BigBIueWhale/sanwu_lasers_magnet_connector/docs/amazon_magnet_diameter_not_as_advertized.jpg

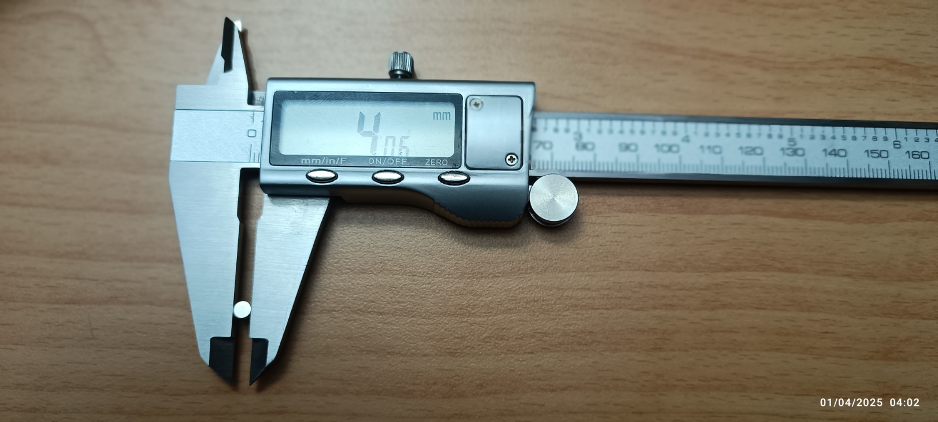
docs/amazon_magnet_diameter_not_as_advertized.jpg
