BigBIueWhale/sanwu_lasers_magnet_connector/docs/bad_super_glue_brand.jpg

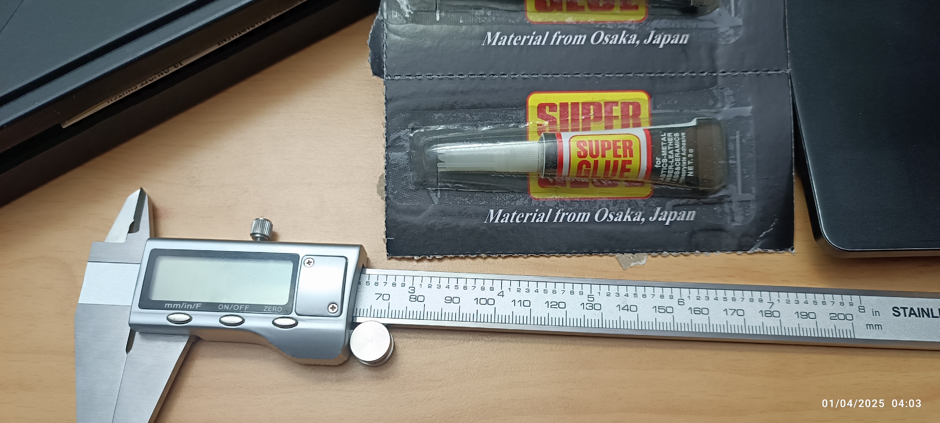
docs/bad_super_glue_brand.jpg
