BigBIueWhale/sanwu_lasers_magnet_connector/docs/gain_leverage.jpg

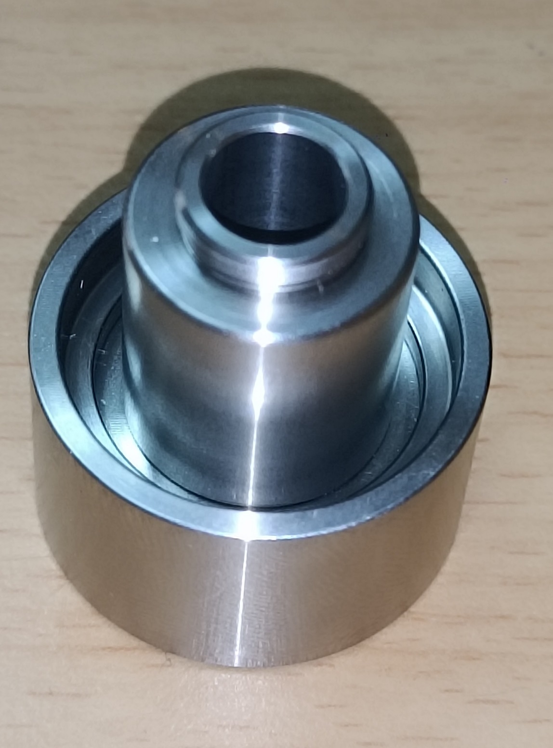
docs/gain_leverage.jpg
