BigBIueWhale/sanwu_lasers_magnet_connector/docs/generic_custom_part_paint_3d_view.png

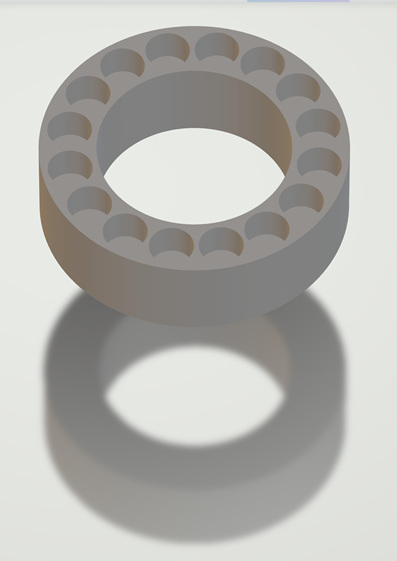
docs/generic_custom_part_paint_3d_view.png
