BigBIueWhale/sanwu_lasers_magnet_connector/docs/good_super_glue_brand.jpg

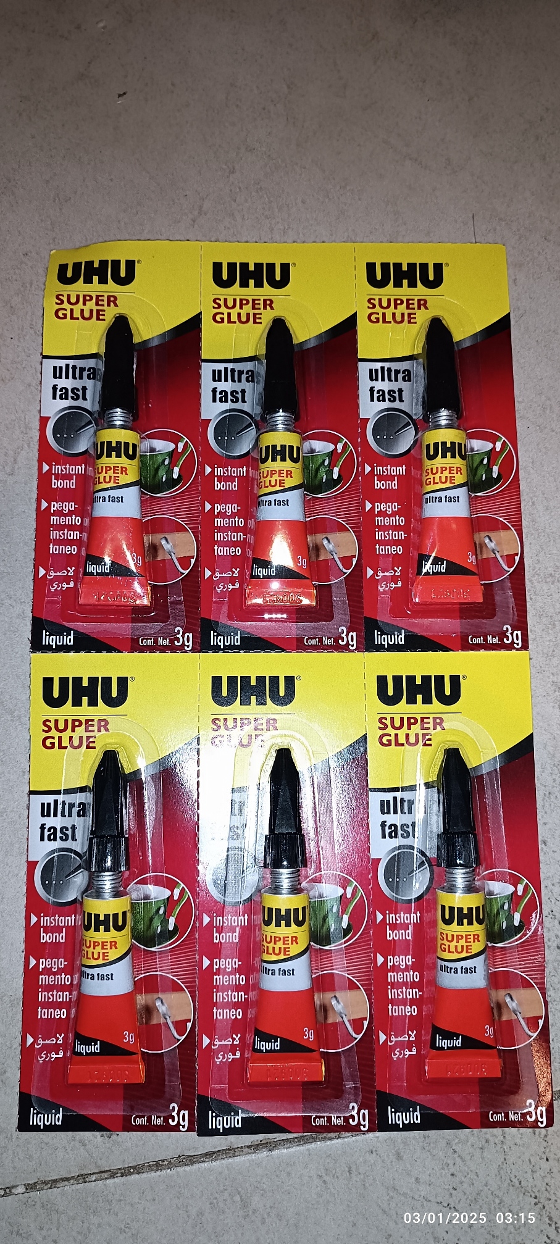
docs/good_super_glue_brand.jpg
