BigBIueWhale/sanwu_lasers_magnet_connector/docs/guard_sleeve_01_00_01_area_to_wipe.jpg

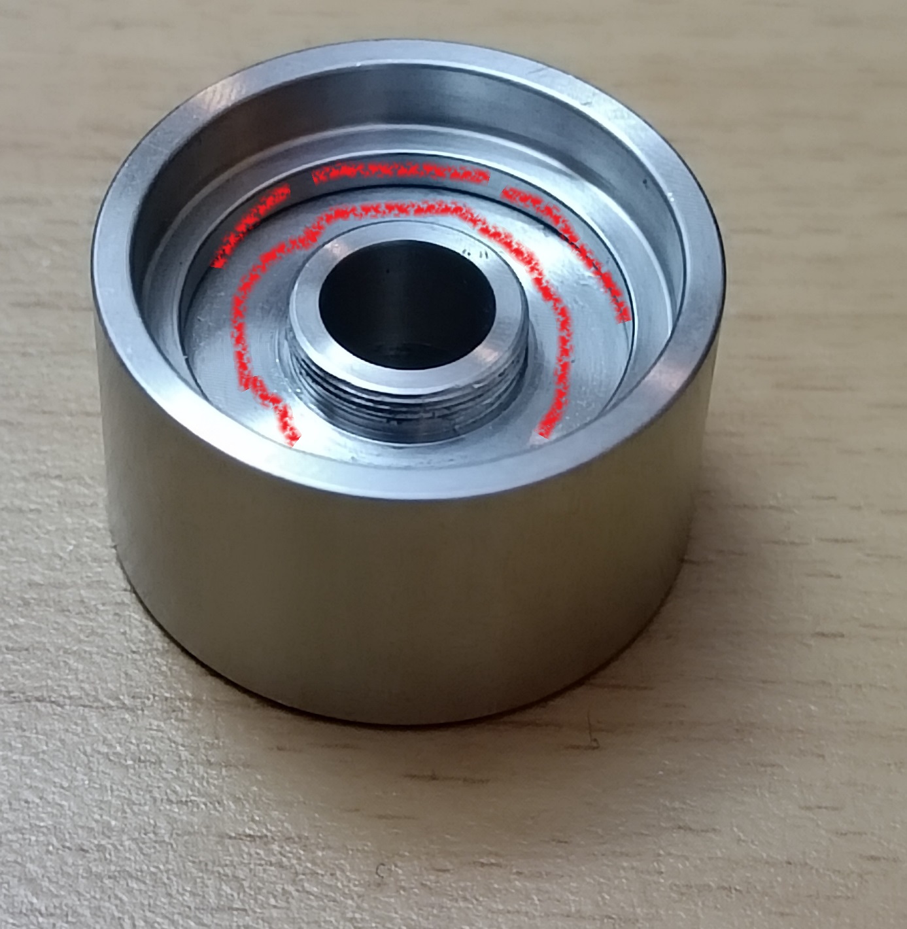
docs/guard_sleeve_01_00_01_area_to_wipe.jpg
