BigBIueWhale/sanwu_lasers_magnet_connector/docs/guard_sleeve_01_00_01_inside_of_bottom_ring.jpg

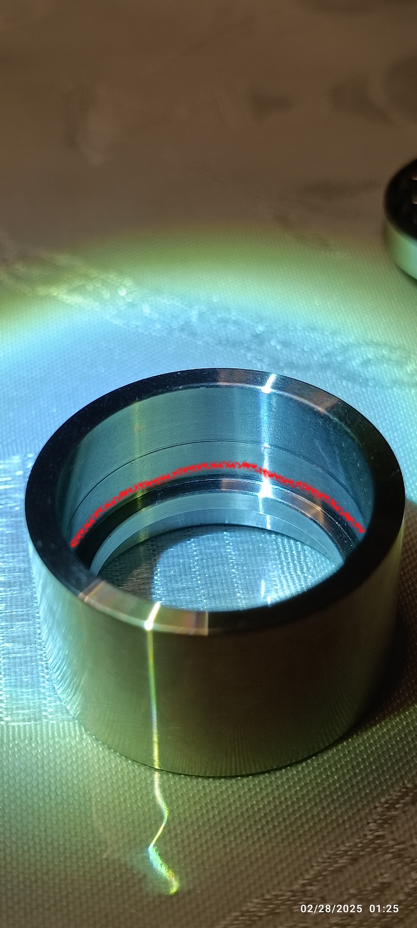
docs/guard_sleeve_01_00_01_inside_of_bottom_ring.jpg
