BigBIueWhale/sanwu_lasers_magnet_connector/docs/guard_sleeve_01_00_01_rangers_head.jpg

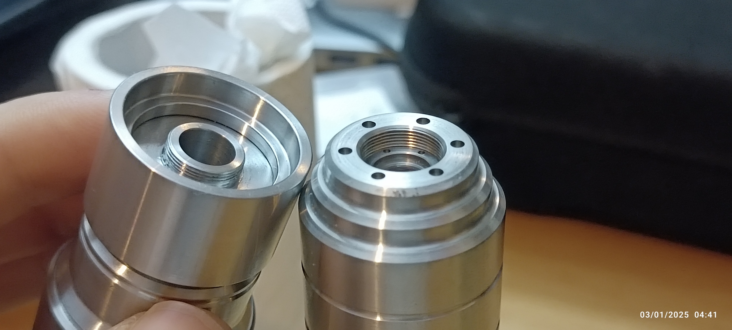
docs/guard_sleeve_01_00_01_rangers_head.jpg
