BigBIueWhale/sanwu_lasers_magnet_connector/docs/laser_and_flashlight_adapter.jpg

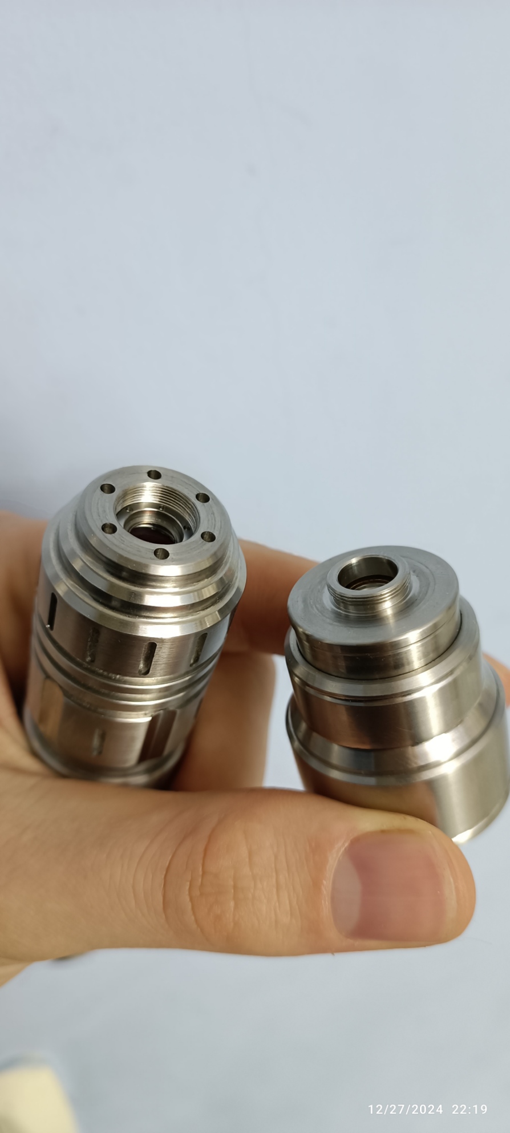
docs/laser_and_flashlight_adapter.jpg
