BigBIueWhale/sanwu_lasers_magnet_connector/docs/laser_rangers_body_models.png

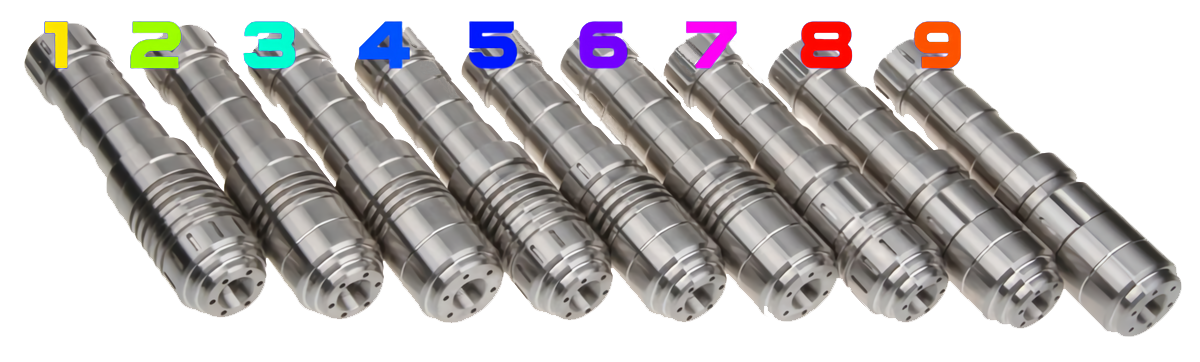
docs/laser_rangers_body_models.png
