BigBIueWhale/sanwu_lasers_magnet_connector/docs/magnets_and_xometry_magnet_holes.jpg

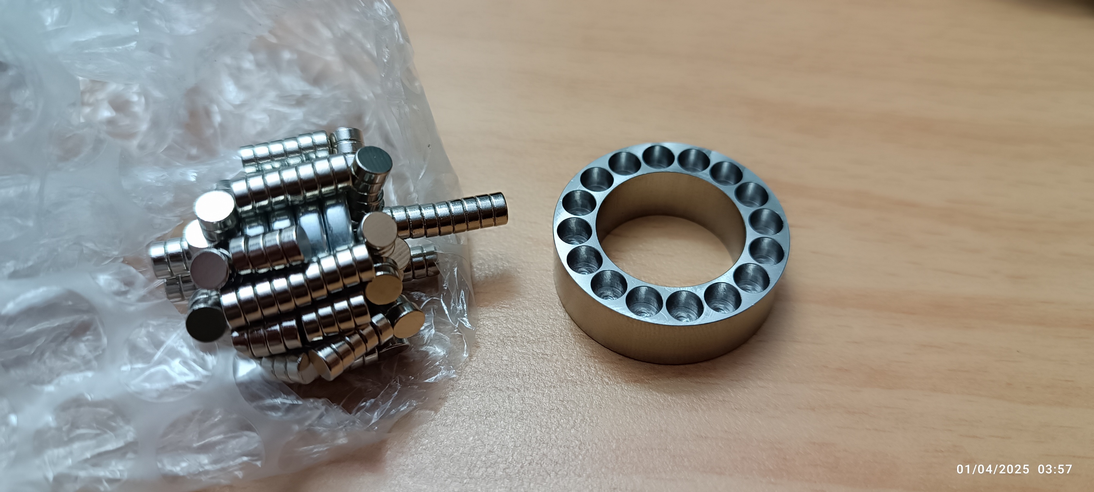
docs/magnets_and_xometry_magnet_holes.jpg
