BigBIueWhale/sanwu_lasers_magnet_connector/docs/magnets_box_findmag.jpg

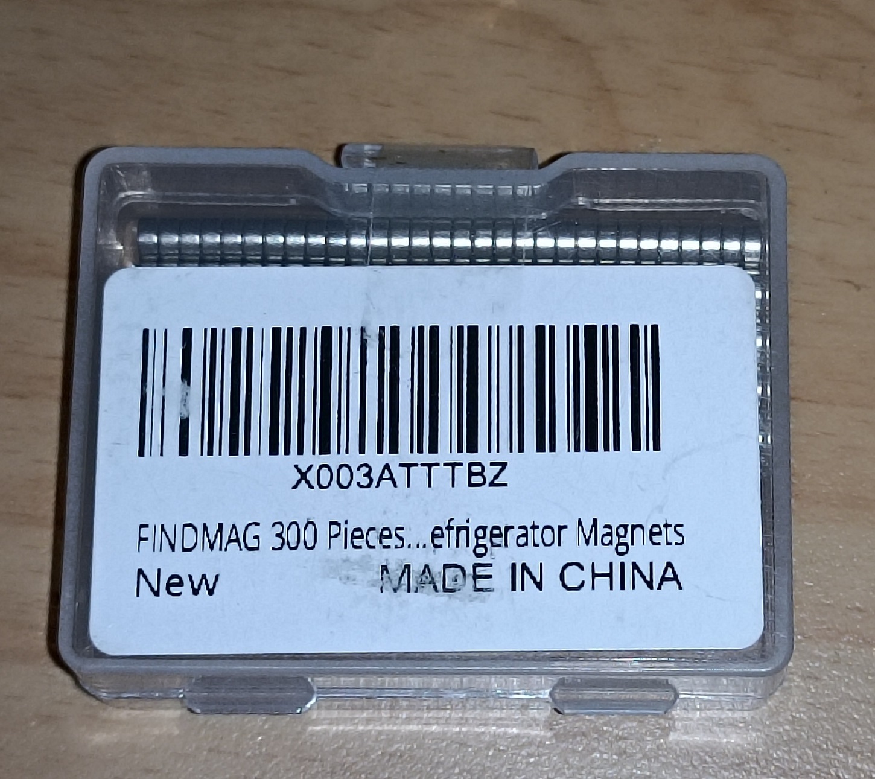
docs/magnets_box_findmag.jpg
