BigBIueWhale/sanwu_lasers_magnet_connector/docs/neodymium_magnets_amazon_listing.png

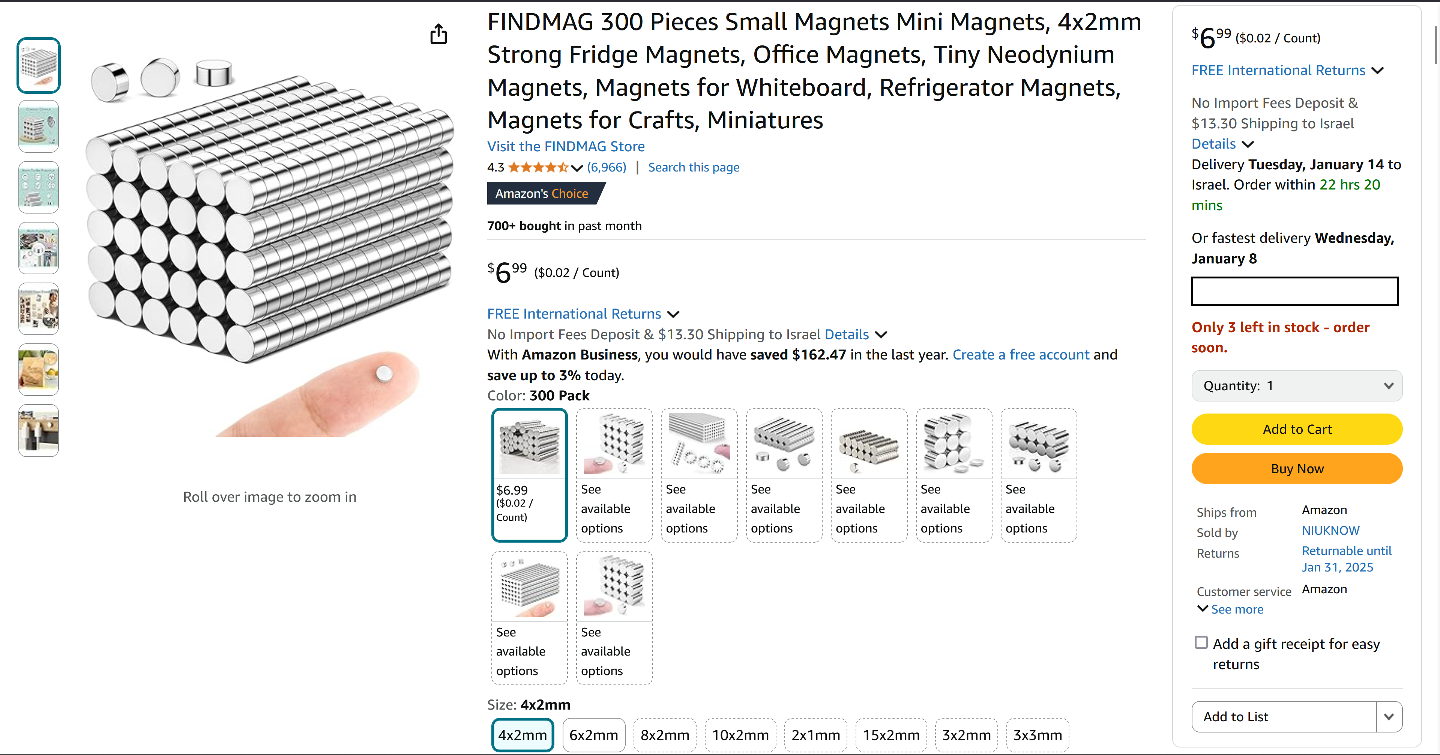
docs/neodymium_magnets_amazon_listing.png
