BigBIueWhale/sanwu_lasers_magnet_connector/docs/pcbway_choose_stainless_steel_303.png

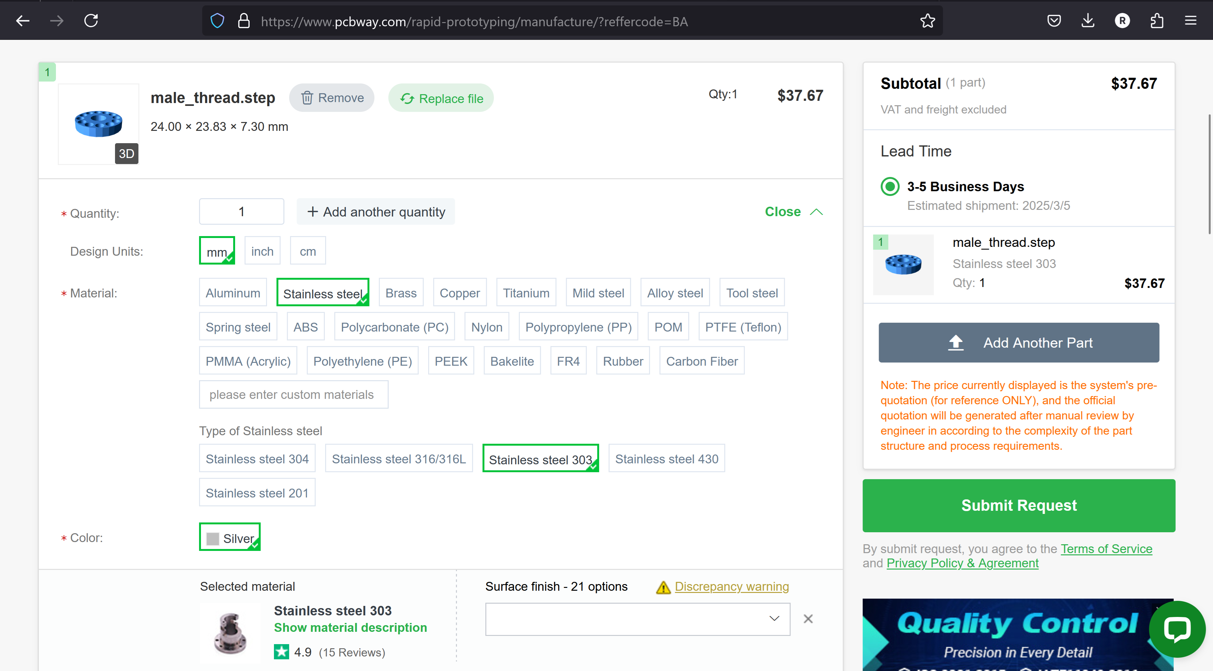
docs/pcbway_choose_stainless_steel_303.png
