BigBIueWhale/sanwu_lasers_magnet_connector/docs/pcbway_click_yes_on_threads_and_tapped_holes.png

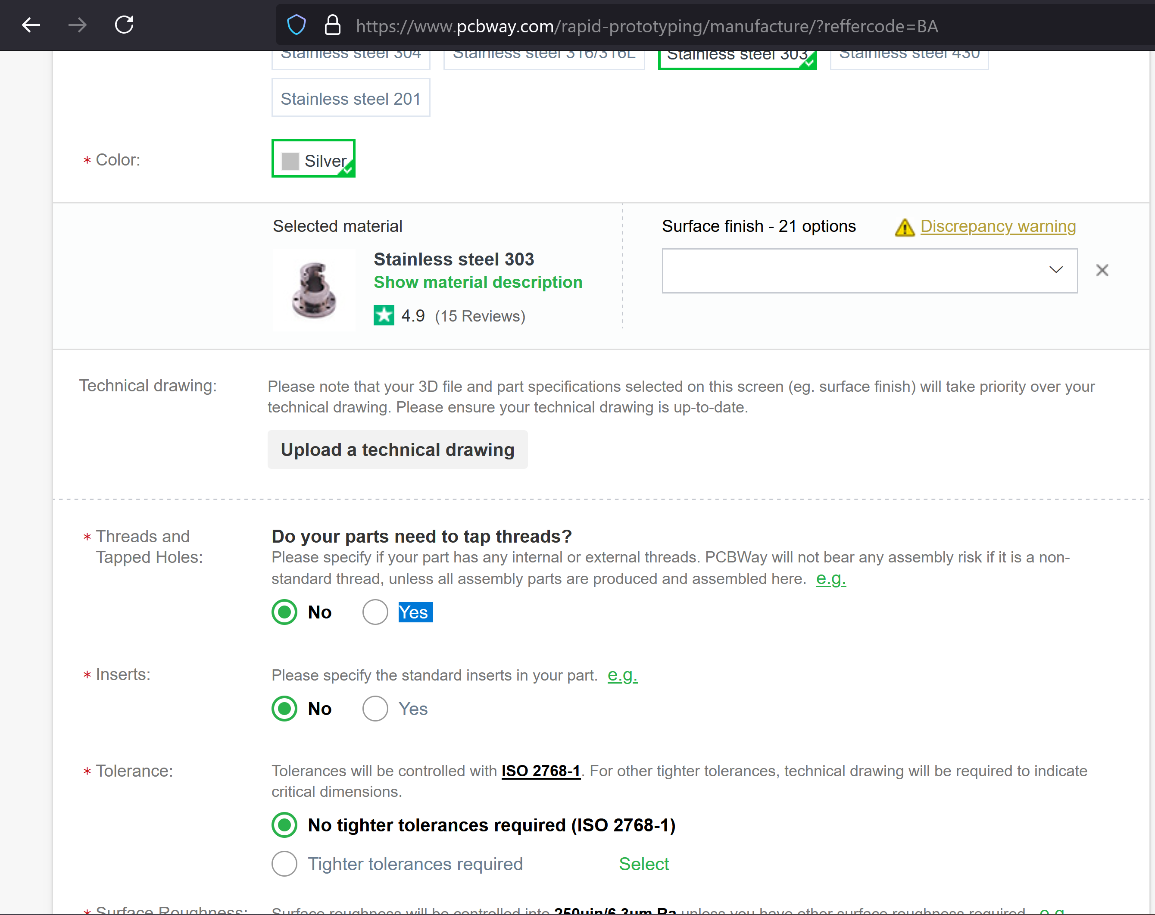
docs/pcbway_click_yes_on_threads_and_tapped_holes.png
