BigBIueWhale/sanwu_lasers_magnet_connector/docs/pcbway_cnc_machining_upload.png

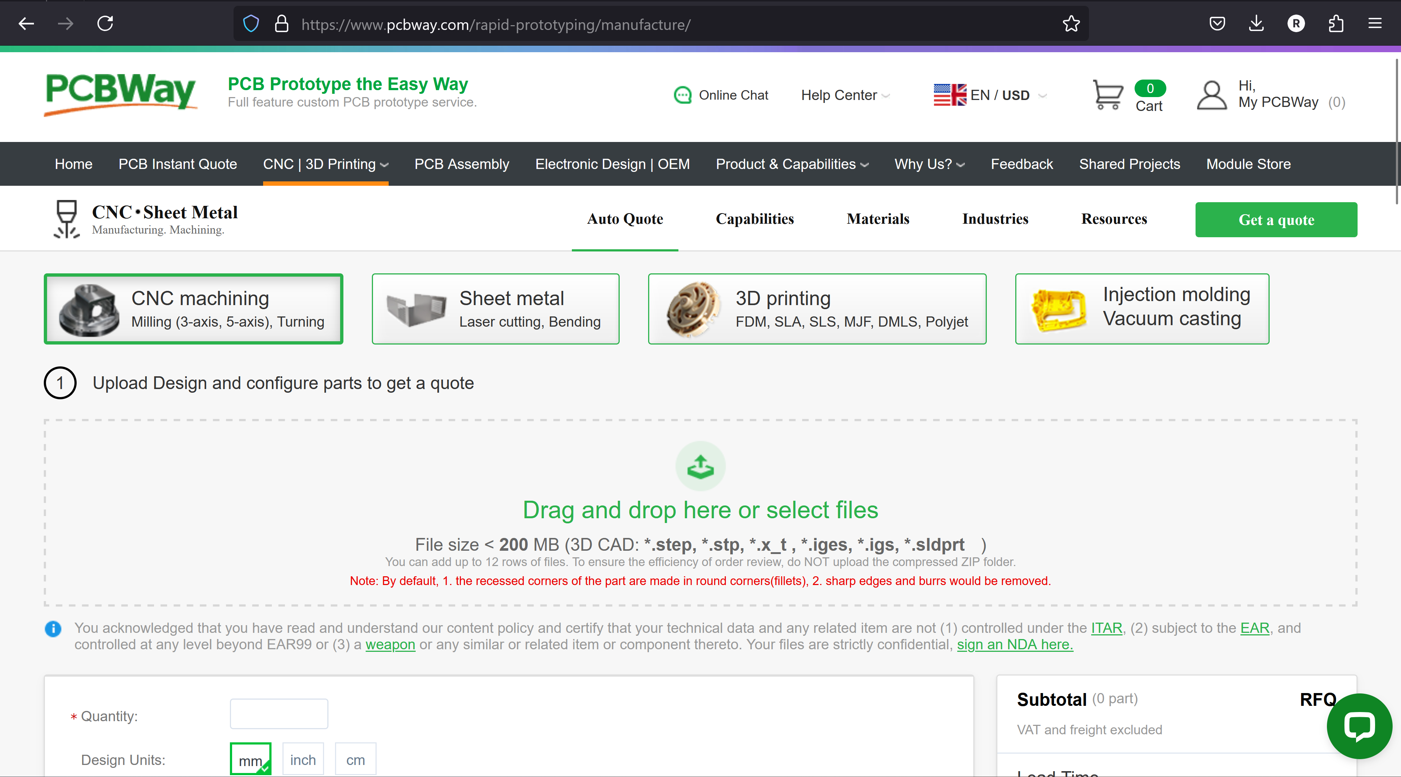
docs/pcbway_cnc_machining_upload.png
