BigBIueWhale/sanwu_lasers_magnet_connector/docs/pcbway_female_thread_01_00_00_raw.jpg

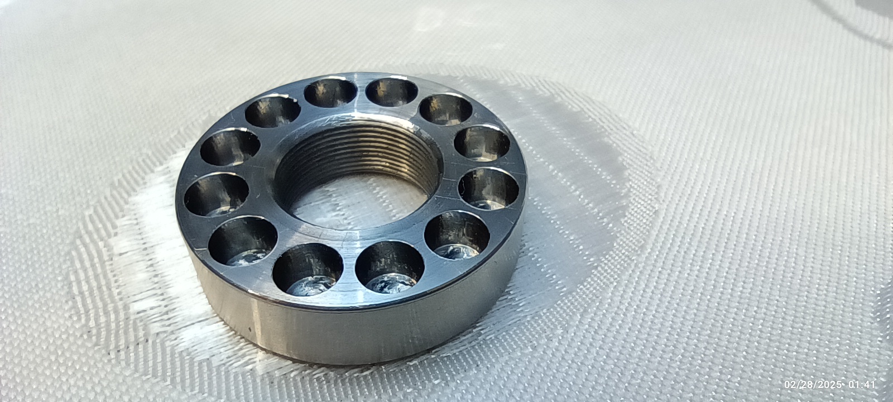
docs/pcbway_female_thread_01_00_00_raw.jpg
