BigBIueWhale/sanwu_lasers_magnet_connector/docs/pcbway_magnet_holes_and_guard_sleeve.jpg

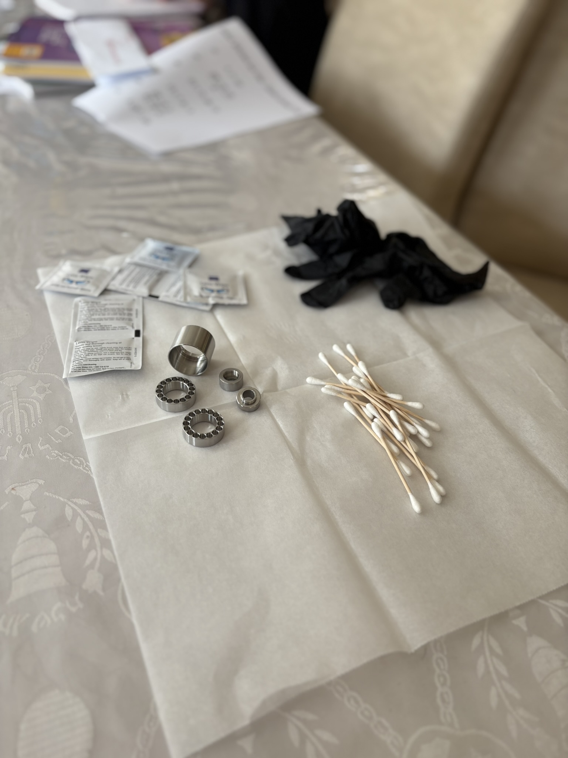
docs/pcbway_magnet_holes_and_guard_sleeve.jpg
