BigBIueWhale/sanwu_lasers_magnet_connector/docs/pcbway_male_female_threads_01_00_00_raw.jpg

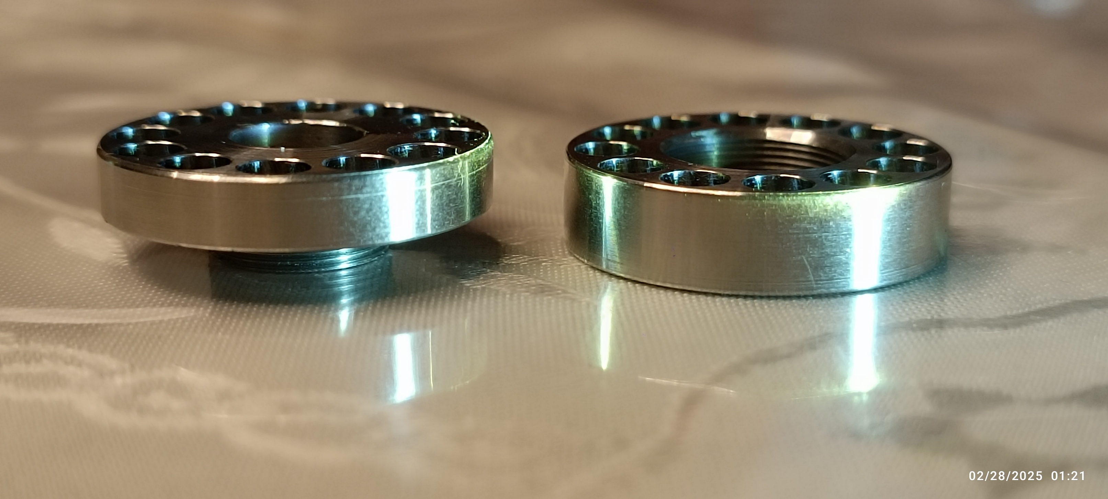
docs/pcbway_male_female_threads_01_00_00_raw.jpg
