BigBIueWhale/sanwu_lasers_magnet_connector/docs/pcbway_male_thread_01_00_00_raw.jpg

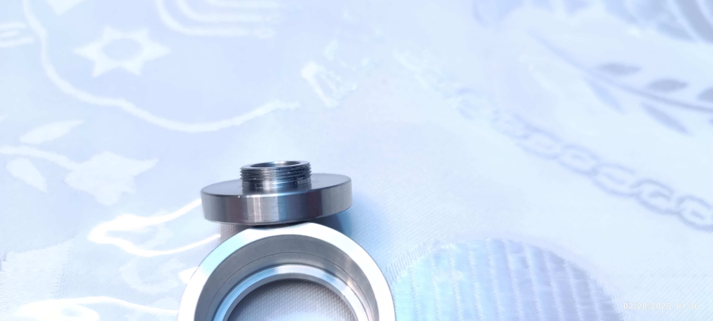
docs/pcbway_male_thread_01_00_00_raw.jpg
