BigBIueWhale/sanwu_lasers_magnet_connector/docs/pcbway_ready_to_submit_request.png

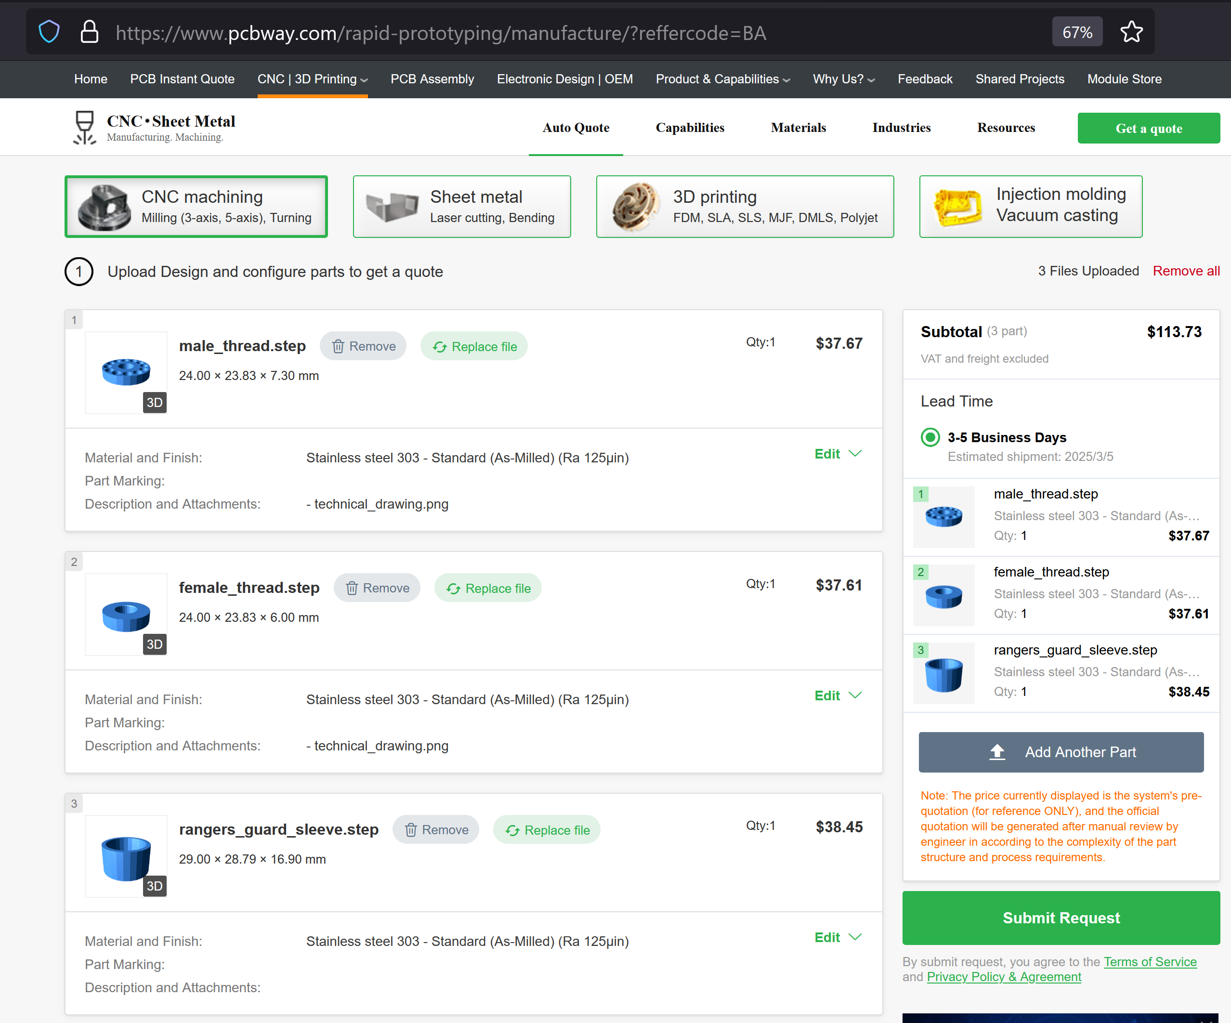
docs/pcbway_ready_to_submit_request.png
