BigBIueWhale/sanwu_lasers_magnet_connector/docs/pcbway_upload_technical_drawing.png

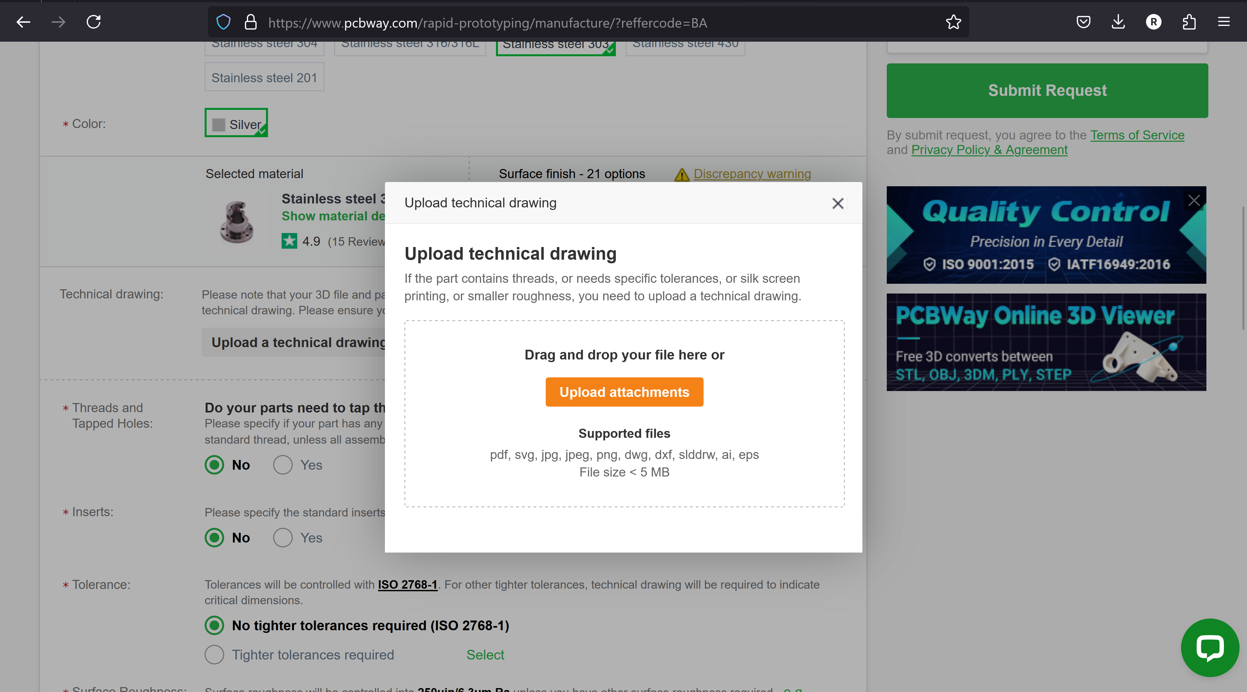
docs/pcbway_upload_technical_drawing.png
