BigBIueWhale/sanwu_lasers_magnet_connector/docs/sanwu_adapter_cut_in_half.jpg

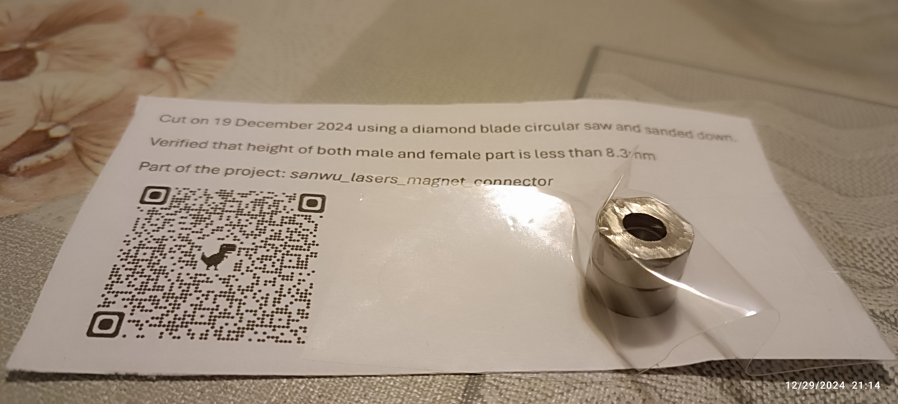
docs/sanwu_adapter_cut_in_half.jpg
