BigBIueWhale/sanwu_lasers_magnet_connector/docs/sanwu_adapter_in_flashlight_converter_listing.png

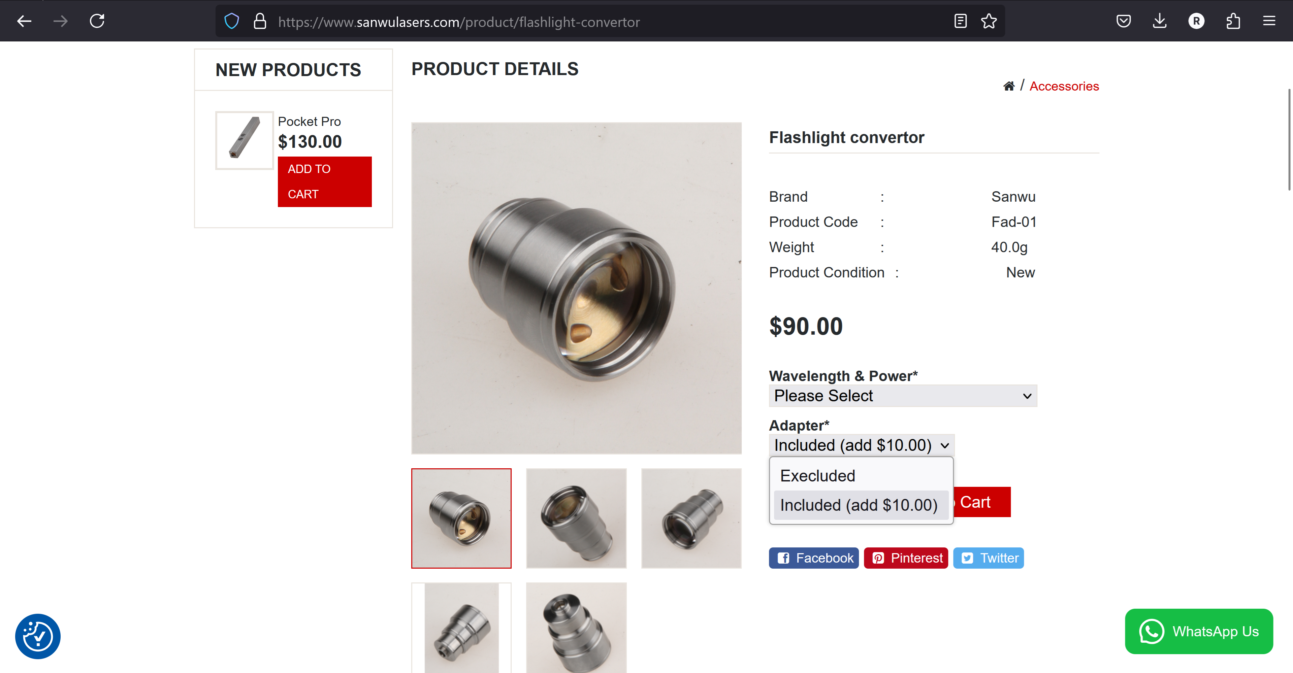
docs/sanwu_adapter_in_flashlight_converter_listing.png
