BigBIueWhale/sanwu_lasers_magnet_connector/docs/sanwu_striker_adapter_female_view.jpg

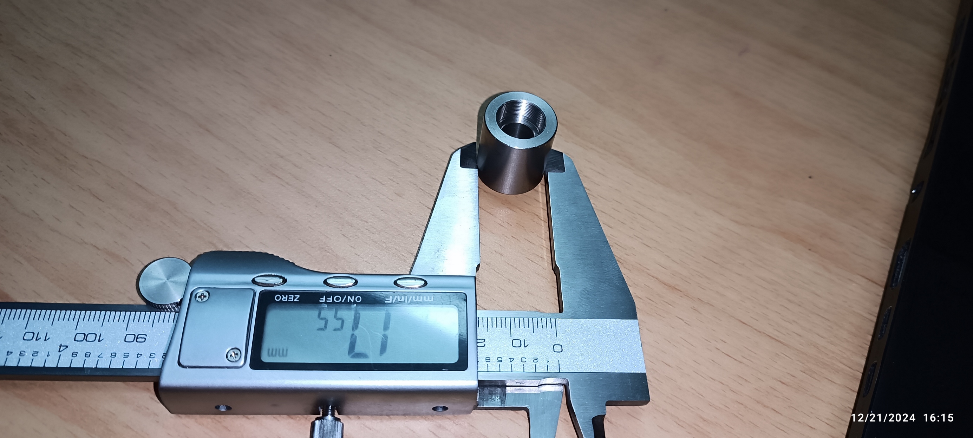
docs/sanwu_striker_adapter_female_view.jpg
