BigBIueWhale/sanwu_lasers_magnet_connector/docs/tight_fit_despite_magnets_slightly_extruding.jpg

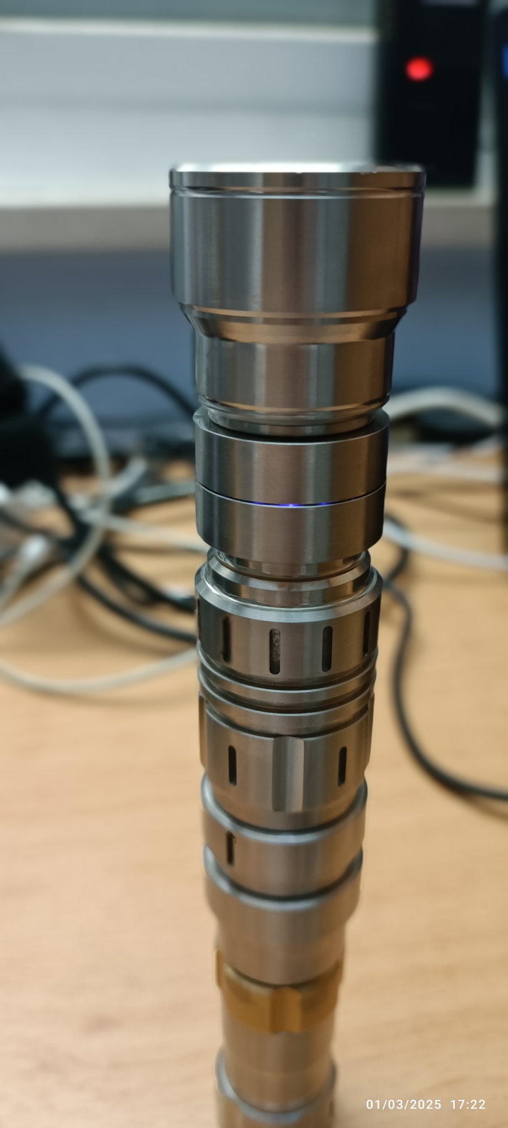
docs/tight_fit_despite_magnets_slightly_extruding.jpg
