BigBIueWhale/sanwu_lasers_magnet_connector/docs/two_stacked_magnets_fit_in_3.3mm_hole_perfectly.jpg

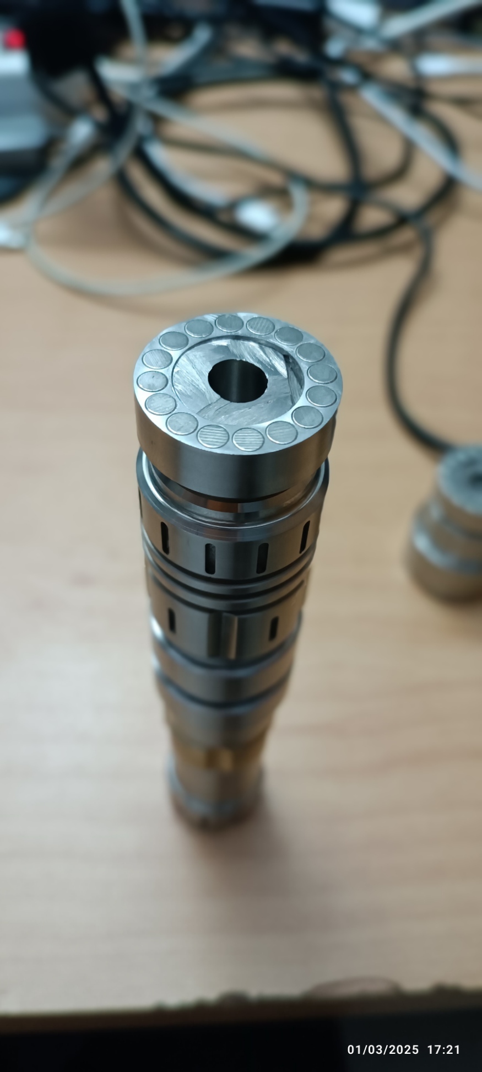
docs/two_stacked_magnets_fit_in_3.3mm_hole_perfectly.jpg
