BigBIueWhale/sanwu_lasers_magnet_connector/female_thread_01_00_00/technical_drawing/isometric_top_view_edited.png

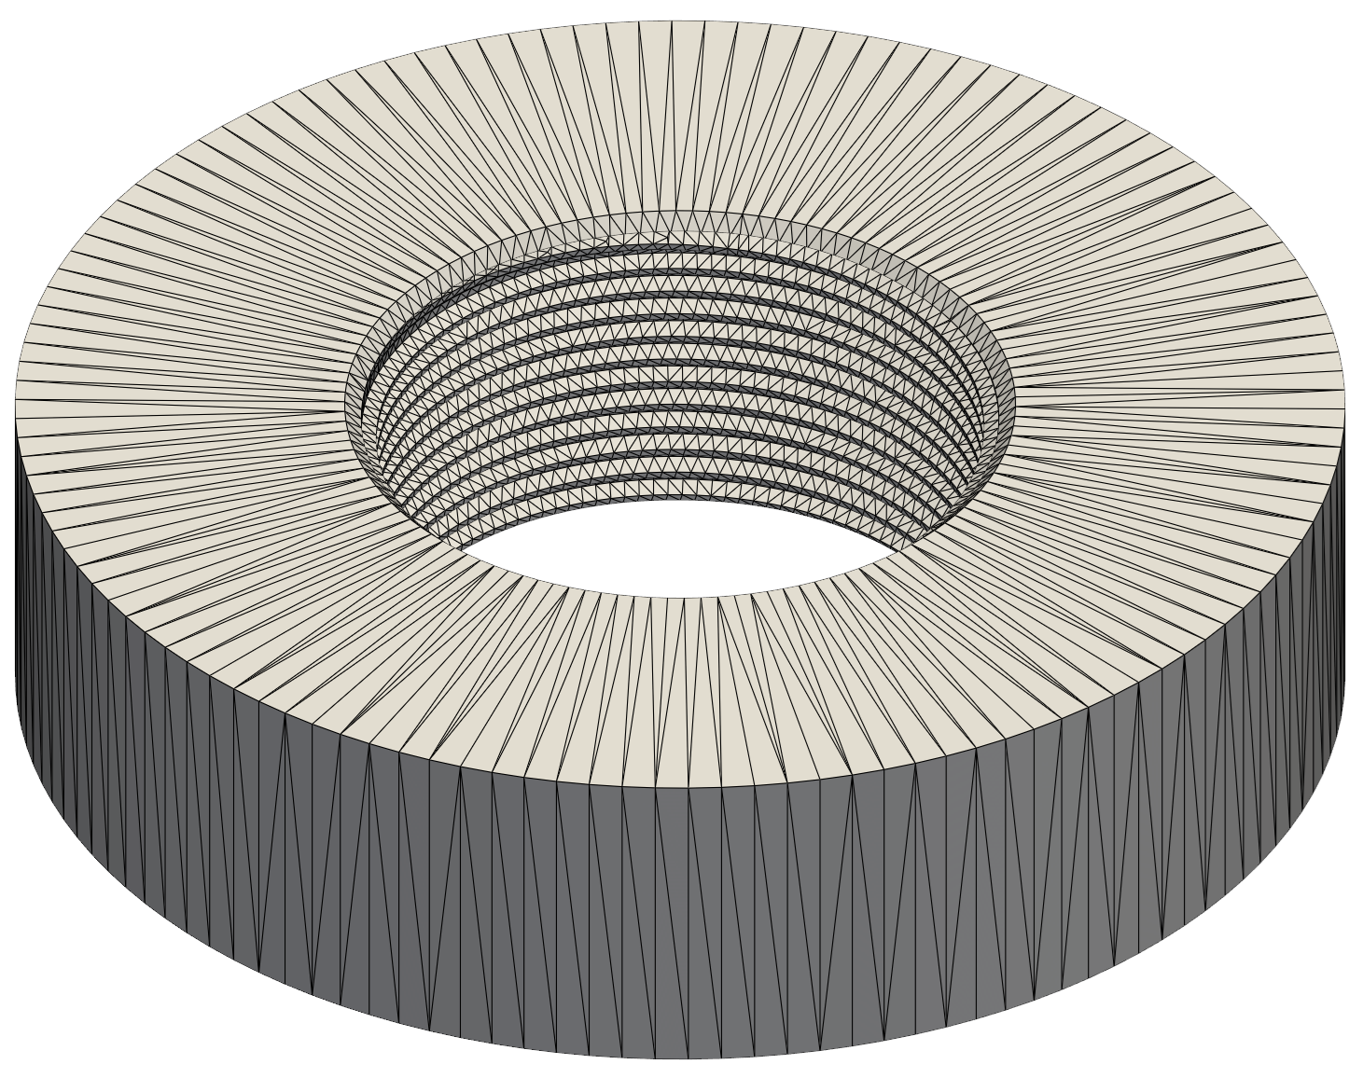
female_thread_01_00_00/technical_drawing/isometric_top_view_edited.png
