BigBIueWhale/sanwu_lasers_magnet_connector/female_thread_01_00_00/technical_drawing/technical_drawing.png

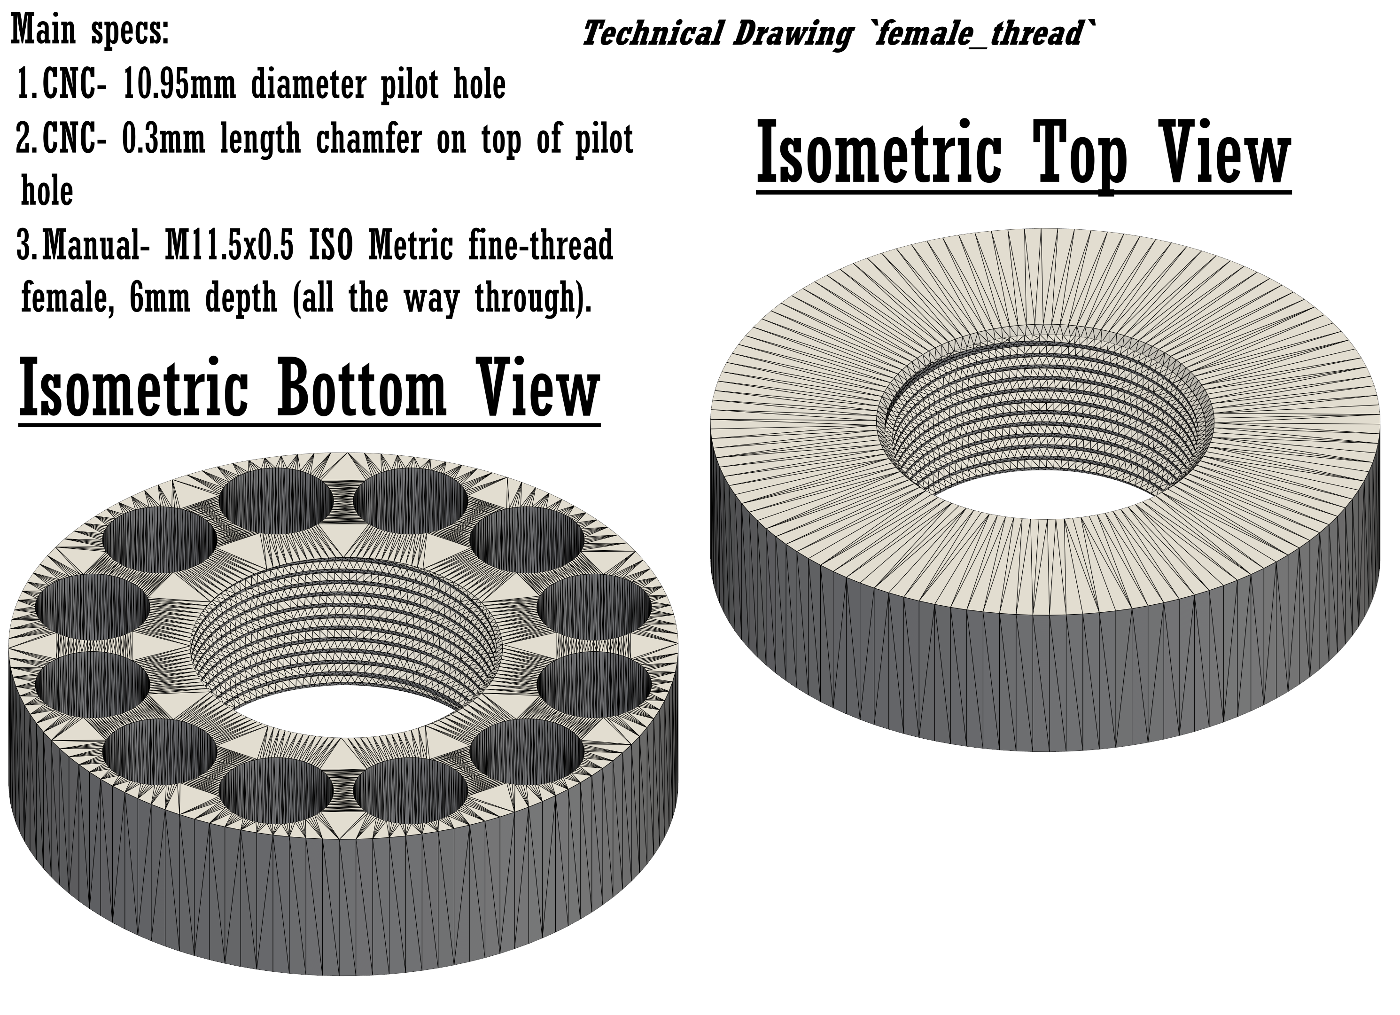
female_thread_01_00_00/technical_drawing/technical_drawing.png
