BigBIueWhale/sanwu_lasers_magnet_connector/male_thread_01_00_00/technical_drawing/bottom_view_noted.png

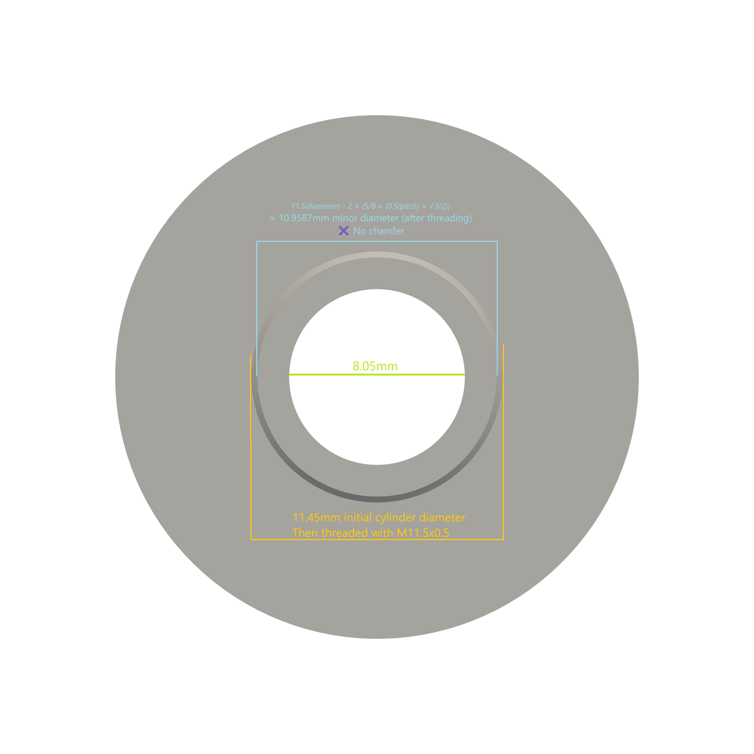
male_thread_01_00_00/technical_drawing/bottom_view_noted.png
