BigBIueWhale/sanwu_lasers_magnet_connector/male_thread_01_00_00/technical_drawing/technical_drawing.png

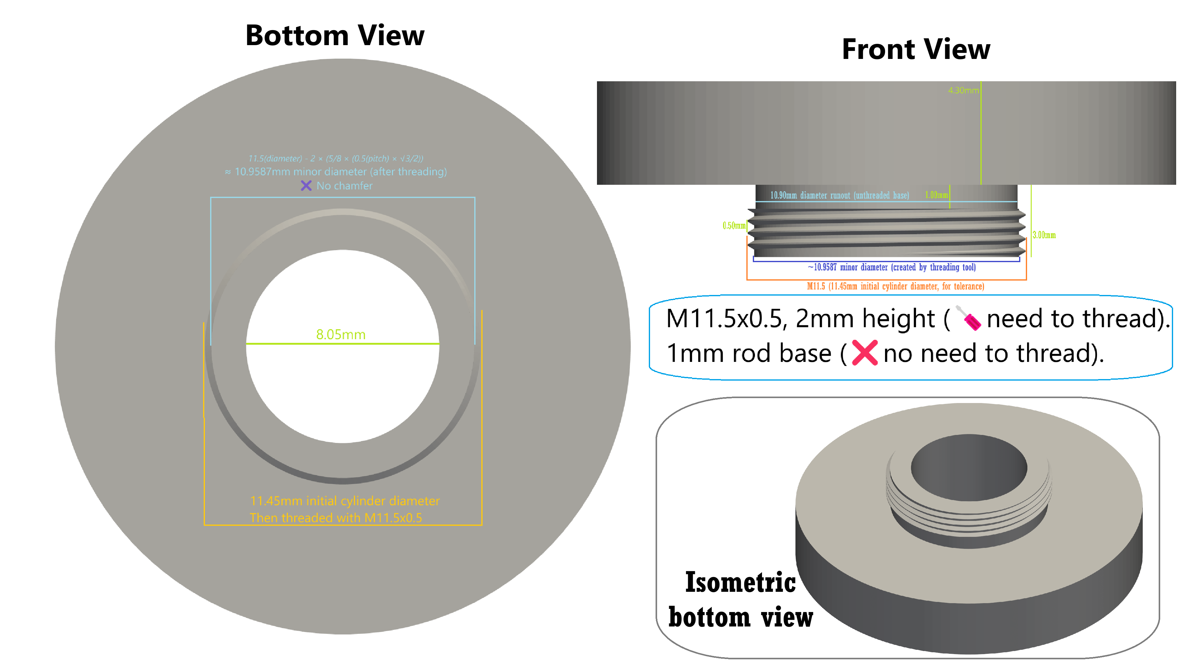
male_thread_01_00_00/technical_drawing/technical_drawing.png
