BigBIueWhale/sanwu_lasers_magnet_connector/docs/pcbway_select_additional_step_files.png

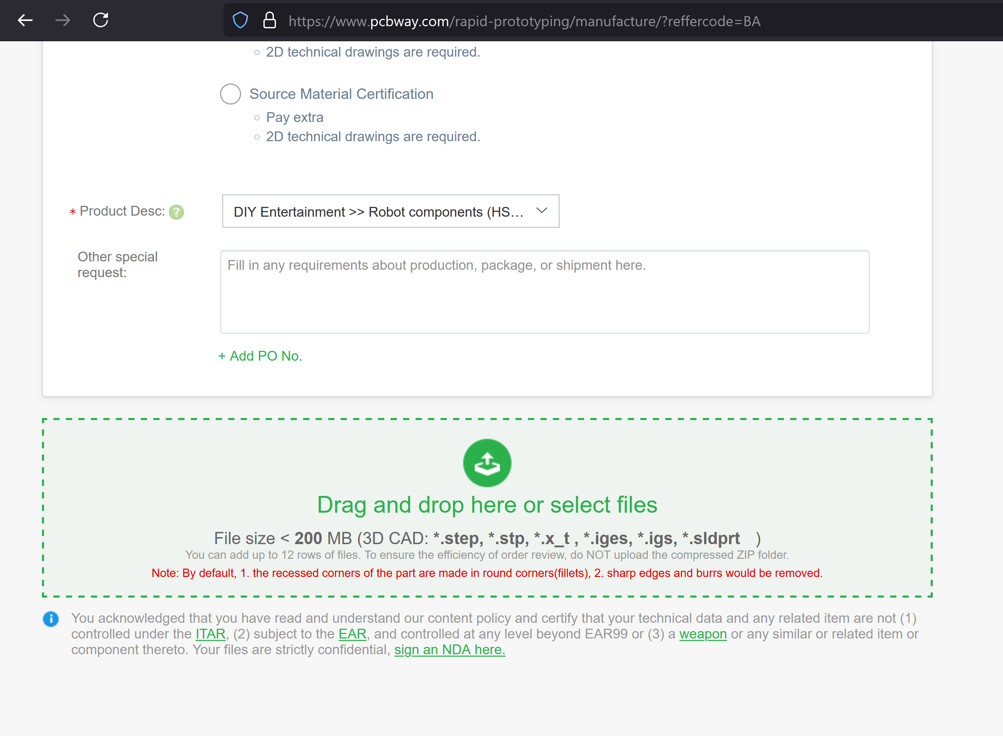
docs/pcbway_select_additional_step_files.png
