BigBIueWhale/sanwu_lasers_magnet_connector/docs/final_xometry_male_and_female_result.jpg

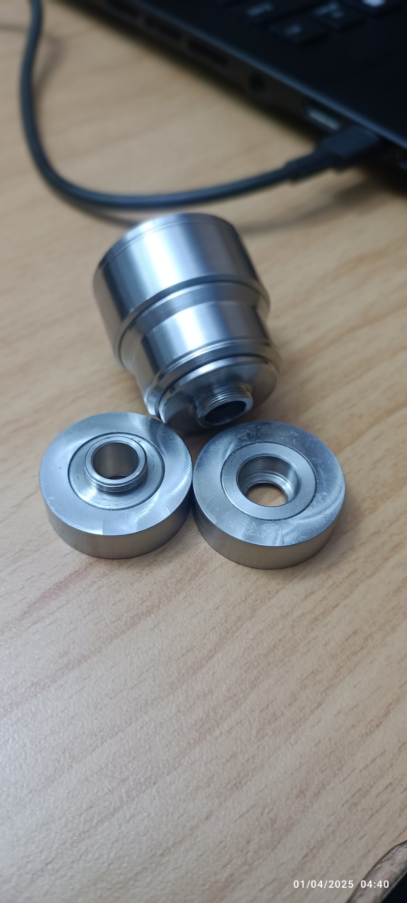
docs/final_xometry_male_and_female_result.jpg
