BigBIueWhale/sanwu_lasers_magnet_connector/docs/final_xometry_male_and_female_result_cropped.png

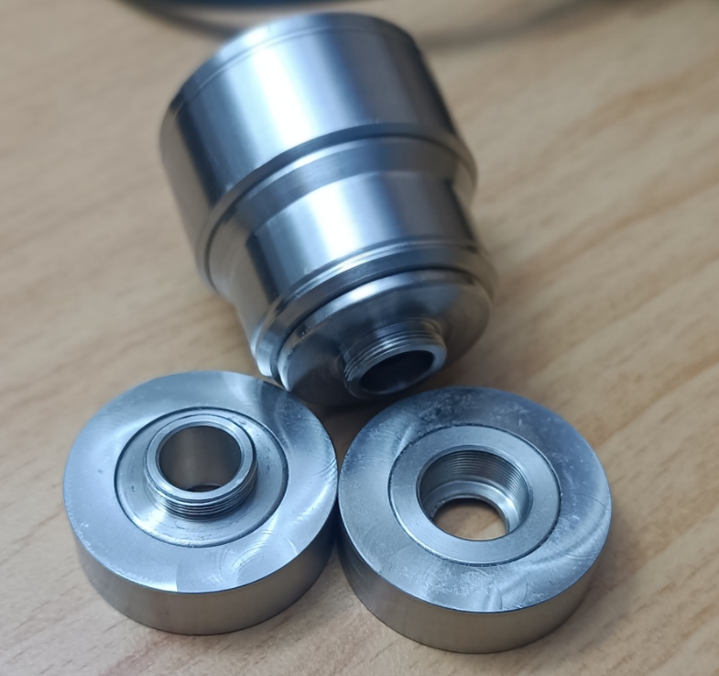
docs/final_xometry_male_and_female_result_cropped.png
