BigBIueWhale/sanwu_lasers_magnet_connector/docs/xometry_final_result.jpg

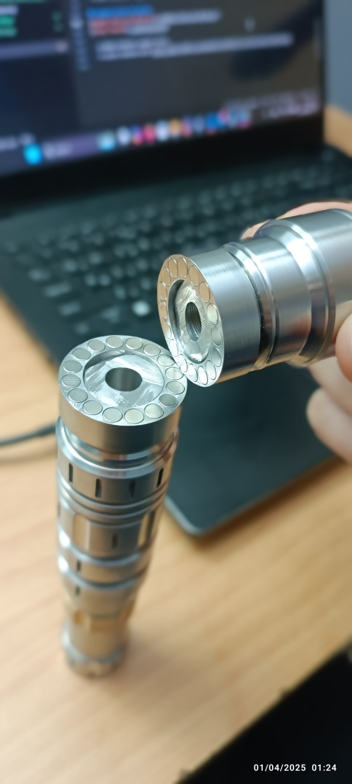
docs/xometry_final_result.jpg
