BigBIueWhale/sanwu_lasers_magnet_connector/docs/xometry_raw_result.jpg

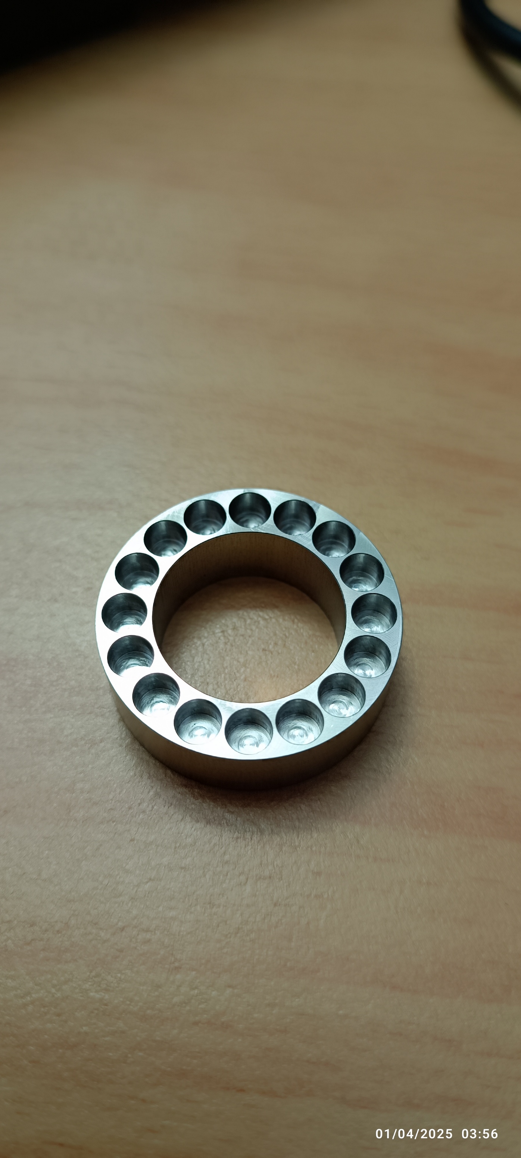
docs/xometry_raw_result.jpg
